faqimuh/TapSit/assets/Tuser.jpg

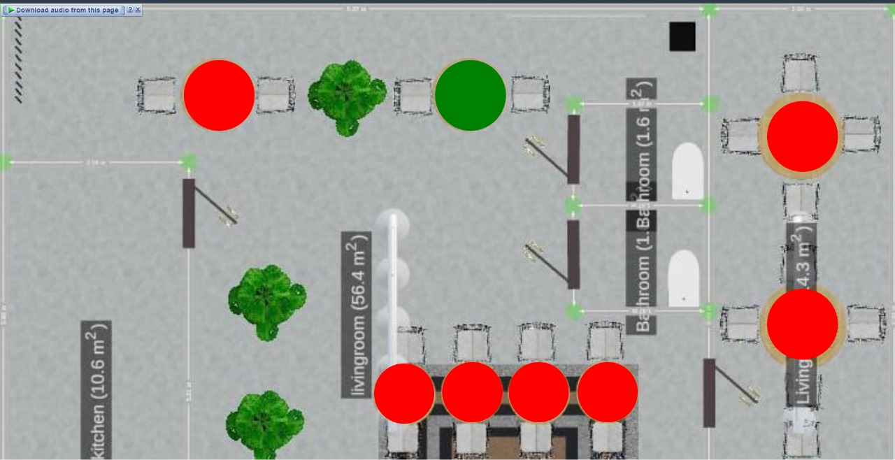
assets/Tuser.jpg
