faqimuh/TapSit/Interface UI/UX/img/about/about.png

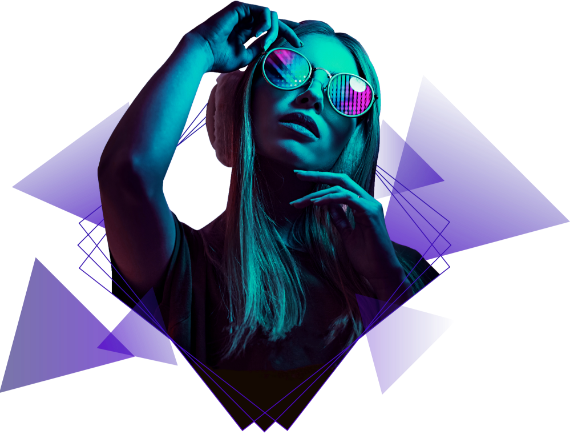
Interface UI/UX/img/about/about.png
