faqimuh/TapSit/Interface UI/UX/img/about/ap-1.jpg

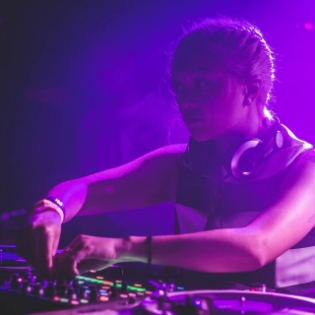
Interface UI/UX/img/about/ap-1.jpg
