faqimuh/TapSit/Interface UI/UX/img/about/ap-2.jpg

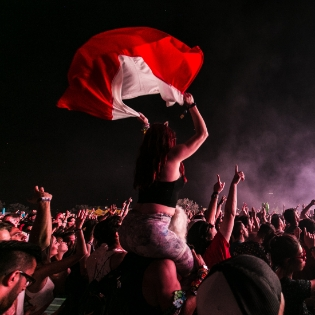
Interface UI/UX/img/about/ap-2.jpg
