faqimuh/TapSit/Interface UI/UX/img/about/ap-3.jpg

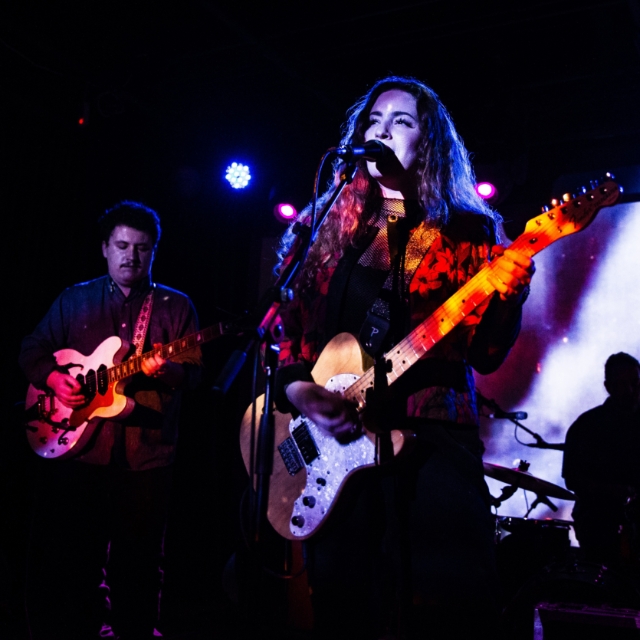
Interface UI/UX/img/about/ap-3.jpg
