faqimuh/TapSit/Interface UI/UX/img/about/ap-4.jpg

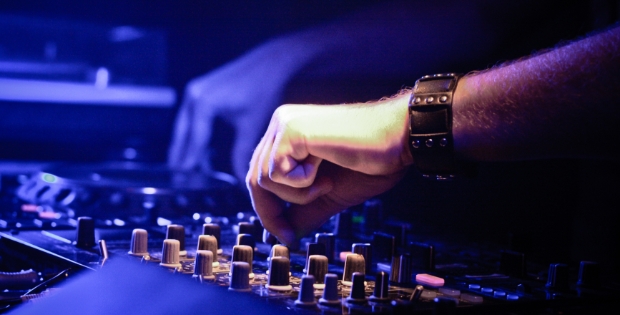
Interface UI/UX/img/about/ap-4.jpg
