faqimuh/TapSit/Interface UI/UX/img/about/ap-5.jpg

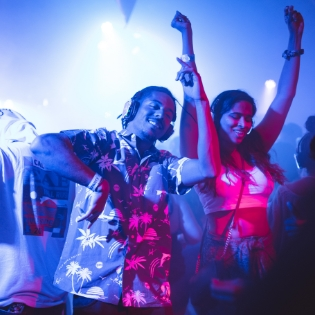
Interface UI/UX/img/about/ap-5.jpg
