faqimuh/TapSit/Interface UI/UX/img/about/ap-6.jpg

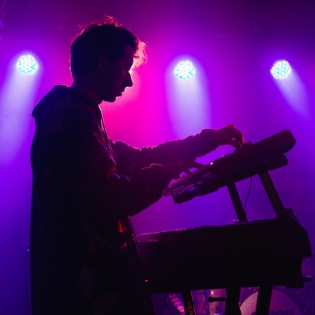
Interface UI/UX/img/about/ap-6.jpg
