faqimuh/TapSit/Interface UI/UX/img/about/ap-7.jpg

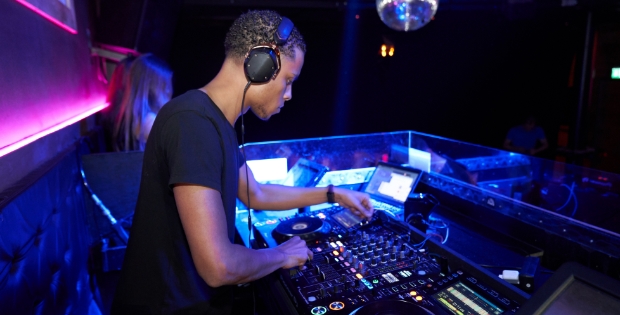
Interface UI/UX/img/about/ap-7.jpg
