faqimuh/TapSit/Interface UI/UX/img/Background.jpg

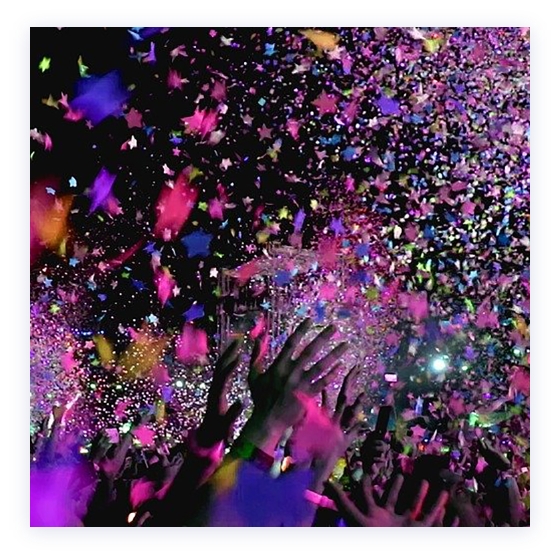
Interface UI/UX/img/Background.jpg
