faqimuh/TapSit/Interface UI/UX/img/blog/blog-1.jpg

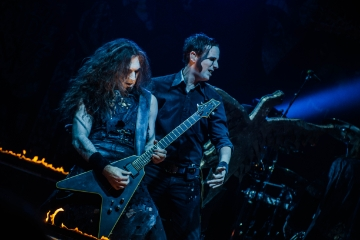
Interface UI/UX/img/blog/blog-1.jpg
