faqimuh/TapSit/Interface UI/UX/img/blog/blog-2.jpg

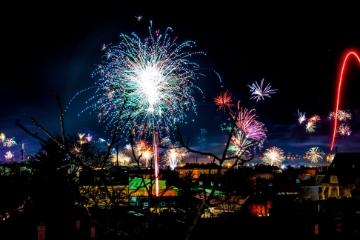
Interface UI/UX/img/blog/blog-2.jpg
