faqimuh/TapSit/Interface UI/UX/img/blog/blog-3.jpg

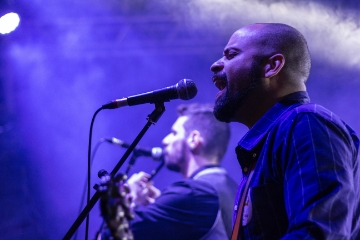
Interface UI/UX/img/blog/blog-3.jpg
