faqimuh/TapSit/Interface UI/UX/img/blog/blog-4.jpg

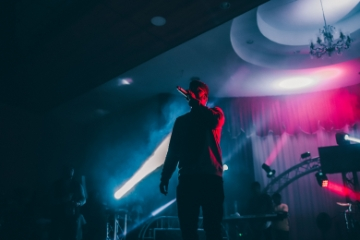
Interface UI/UX/img/blog/blog-4.jpg
