faqimuh/TapSit/Interface UI/UX/img/blog/blog-5.jpg

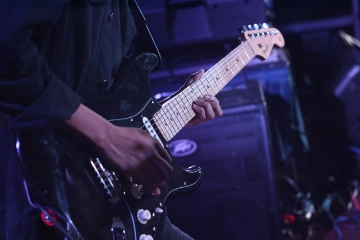
Interface UI/UX/img/blog/blog-5.jpg
