faqimuh/TapSit/Interface UI/UX/img/blog/blog-6.jpg

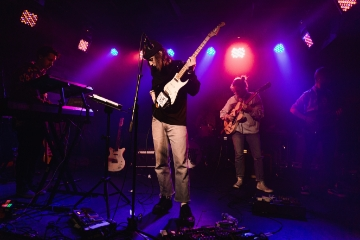
Interface UI/UX/img/blog/blog-6.jpg
