faqimuh/TapSit/Interface UI/UX/img/blog/details/bs-2.jpg

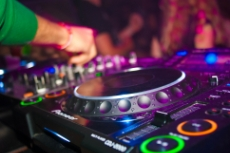
Interface UI/UX/img/blog/details/bs-2.jpg
