faqimuh/TapSit/Interface UI/UX/img/blog/details/details-pic.jpg

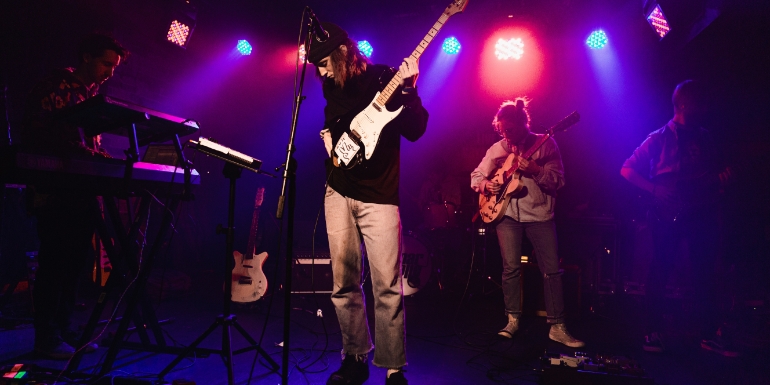
Interface UI/UX/img/blog/details/details-pic.jpg
