faqimuh/TapSit/Interface UI/UX/img/blog/large-item.jpg

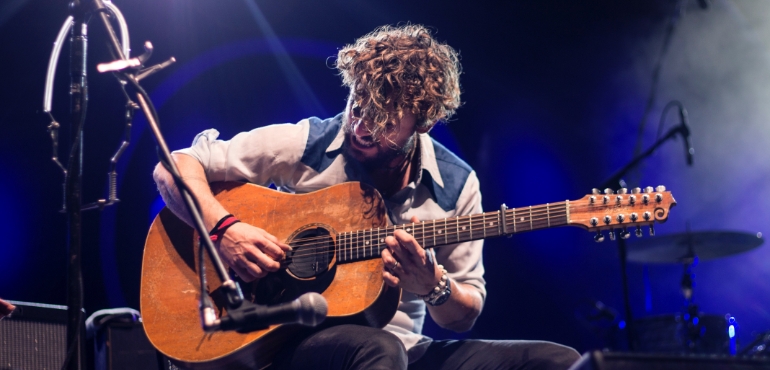
Interface UI/UX/img/blog/large-item.jpg
