faqimuh/TapSit/Interface UI/UX/img/countdown-bg.jpg

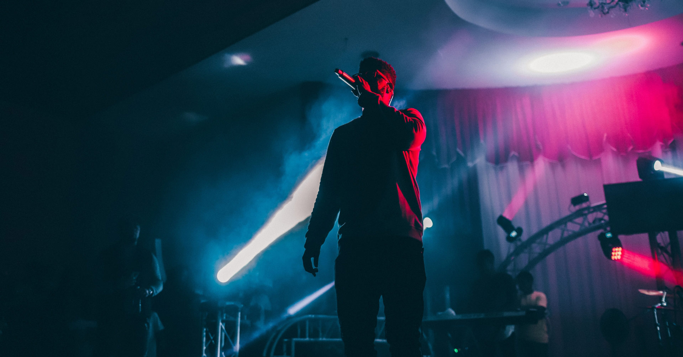
Interface UI/UX/img/countdown-bg.jpg
