faqimuh/TapSit/Interface UI/UX/img/discography/disco-1.jpg

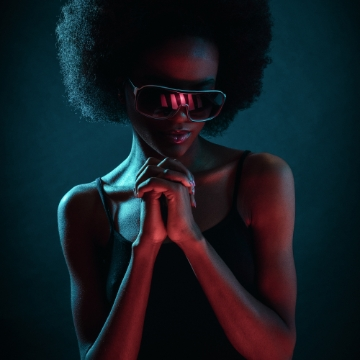
Interface UI/UX/img/discography/disco-1.jpg
