faqimuh/TapSit/Interface UI/UX/img/discography/disco-2.jpg

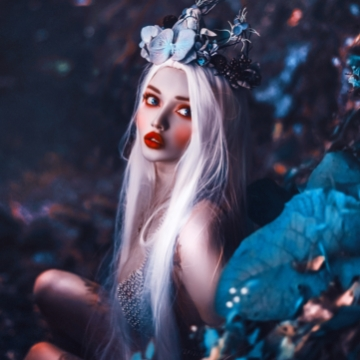
Interface UI/UX/img/discography/disco-2.jpg
