faqimuh/TapSit/Interface UI/UX/img/discography/disco-3.jpg

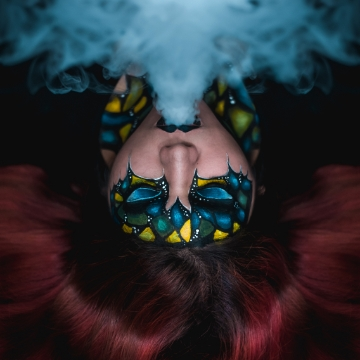
Interface UI/UX/img/discography/disco-3.jpg
