faqimuh/TapSit/Interface UI/UX/img/discography/disco-4.jpg

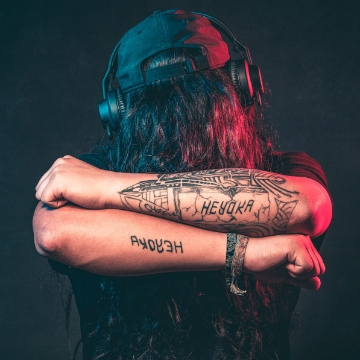
Interface UI/UX/img/discography/disco-4.jpg
