faqimuh/TapSit/Interface UI/UX/img/discography/disco-5.jpg

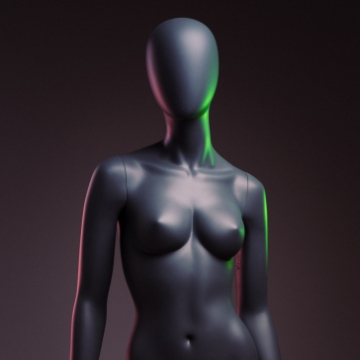
Interface UI/UX/img/discography/disco-5.jpg
