faqimuh/TapSit/Interface UI/UX/img/discography/disco-6.jpg

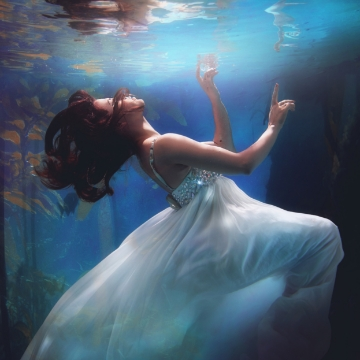
Interface UI/UX/img/discography/disco-6.jpg
