faqimuh/TapSit/Interface UI/UX/img/events/event-1.jpg

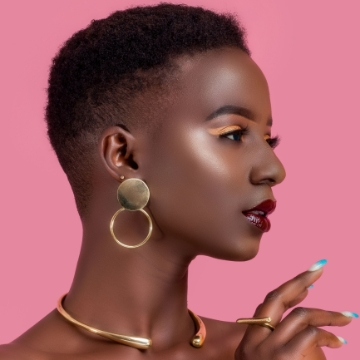
Interface UI/UX/img/events/event-1.jpg
