faqimuh/TapSit/Interface UI/UX/img/events/event-2.jpg

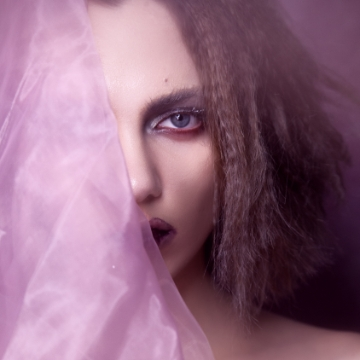
Interface UI/UX/img/events/event-2.jpg
