faqimuh/TapSit/Interface UI/UX/img/events/event-3.jpg

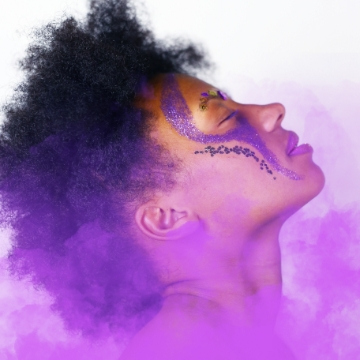
Interface UI/UX/img/events/event-3.jpg
