faqimuh/TapSit/Interface UI/UX/img/footer-bg.png

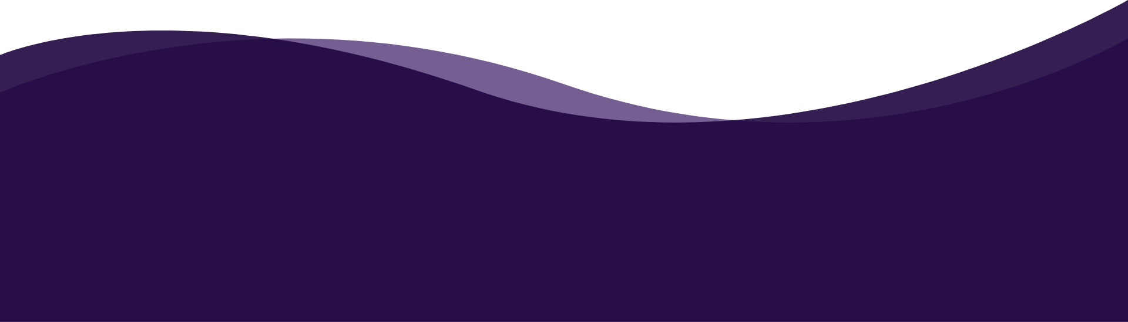
Interface UI/UX/img/footer-bg.png
