faqimuh/TapSit/Interface UI/UX/img/hero-bg.png

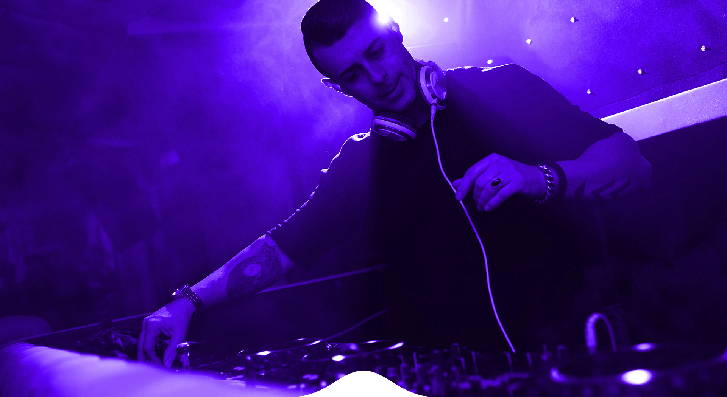
Interface UI/UX/img/hero-bg.png
