faqimuh/TapSit/Interface UI/UX/img/services/as-1.jpg

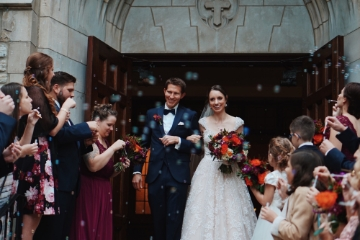
Interface UI/UX/img/services/as-1.jpg
