faqimuh/TapSit/Interface UI/UX/img/services/as-2.jpg

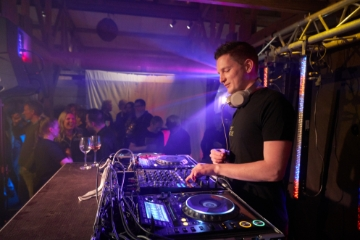
Interface UI/UX/img/services/as-2.jpg
