faqimuh/TapSit/Interface UI/UX/img/services/as-3.jpg

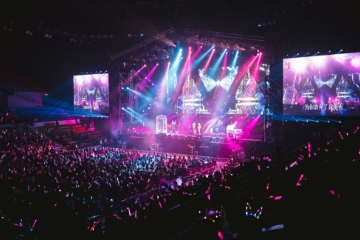
Interface UI/UX/img/services/as-3.jpg
