faqimuh/TapSit/Interface UI/UX/img/skill-video.jpg

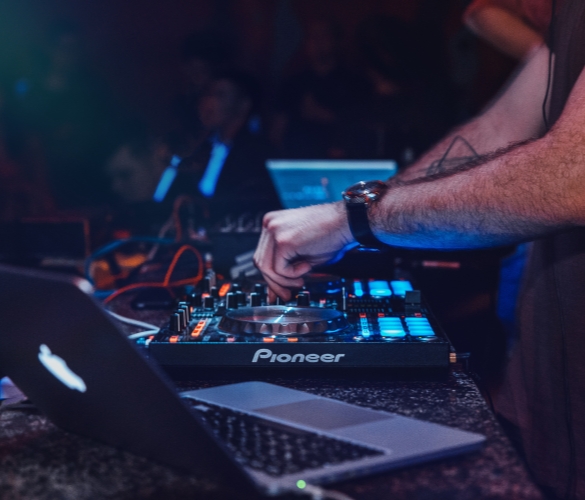
Interface UI/UX/img/skill-video.jpg
