faqimuh/TapSit/Interface UI/UX/img/tours/tour-1.jpg

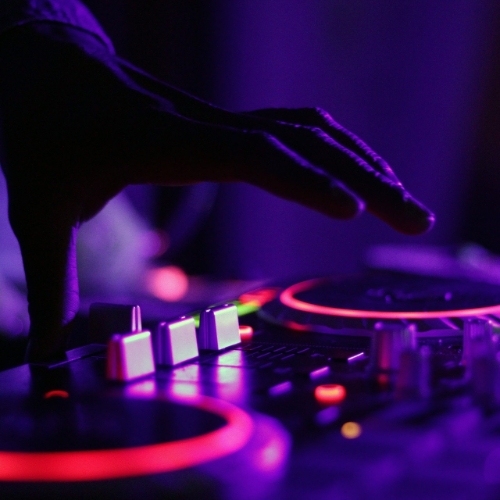
Interface UI/UX/img/tours/tour-1.jpg
