faqimuh/TapSit/Interface UI/UX/img/tours/tour-2.jpg

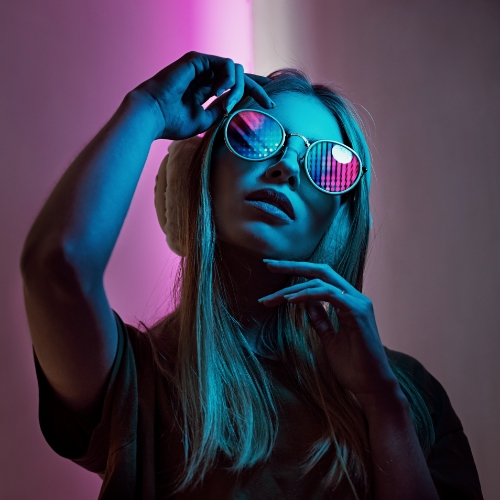
Interface UI/UX/img/tours/tour-2.jpg
