faqimuh/TapSit/Interface UI/UX/img/tours/tour-3.jpg

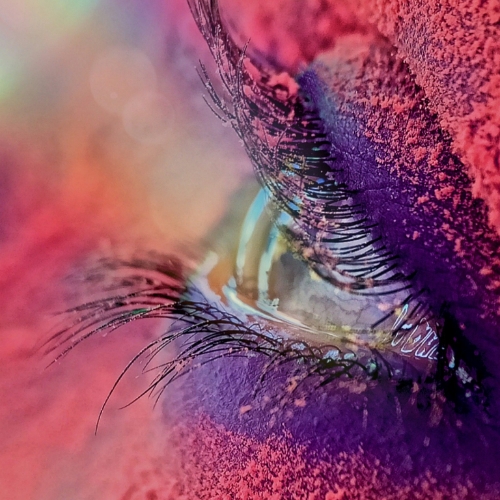
Interface UI/UX/img/tours/tour-3.jpg
