faqimuh/TapSit/Interface UI/UX/img/track-right.jpg

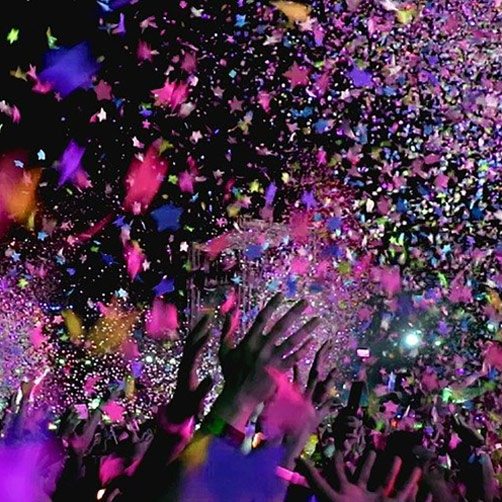
Interface UI/UX/img/track-right.jpg
