faqimuh/TapSit/Interface UI/UX/img/videos/large-item.jpg

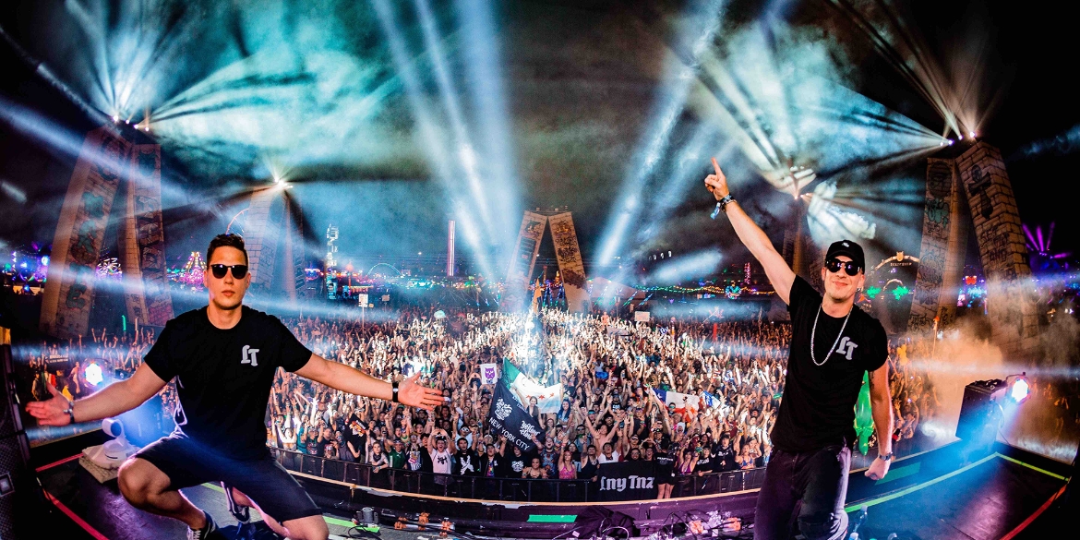
Interface UI/UX/img/videos/large-item.jpg
