faqimuh/TapSit/Interface UI/UX/img/videos/videos-1.jpg

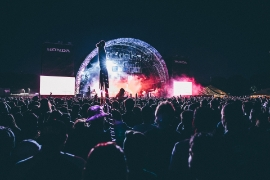
Interface UI/UX/img/videos/videos-1.jpg
