faqimuh/TapSit/Interface UI/UX/img/videos/videos-2.jpg

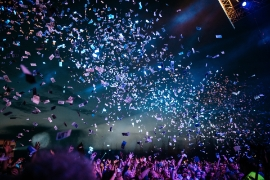
Interface UI/UX/img/videos/videos-2.jpg
