faqimuh/TapSit/Interface UI/UX/img/videos/videos-3.jpg

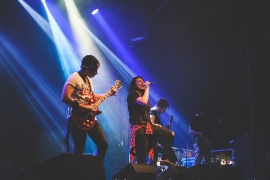
Interface UI/UX/img/videos/videos-3.jpg
