faqimuh/TapSit/Interface UI/UX/img/videos/videos-4.jpg

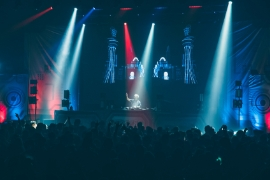
Interface UI/UX/img/videos/videos-4.jpg
