faqimuh/TapSit/Interface UI/UX/img/youtube/youtube-1.jpg

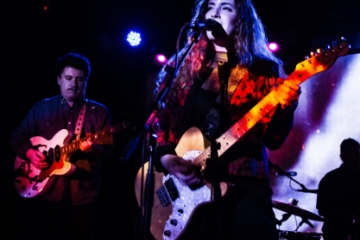
Interface UI/UX/img/youtube/youtube-1.jpg
