faqimuh/TapSit/Interface UI/UX/img/youtube/youtube-2.jpg

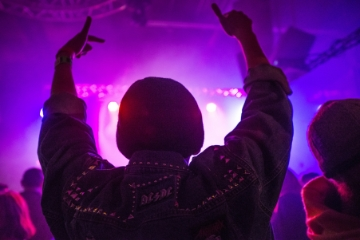
Interface UI/UX/img/youtube/youtube-2.jpg
