faqimuh/TapSit/Interface UI/UX/img/youtube/youtube-3.jpg

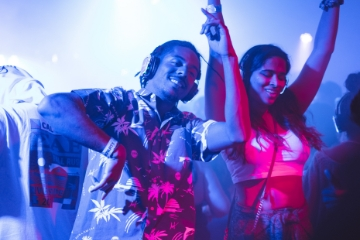
Interface UI/UX/img/youtube/youtube-3.jpg
