faqimuh/TapSit/Interface UI/UX/build/assets/img/4.png

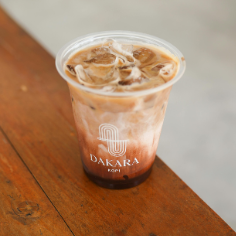
Interface UI/UX/build/assets/img/4.png
