faqimuh/TapSit/Interface UI/UX/build/assets/img/5.png

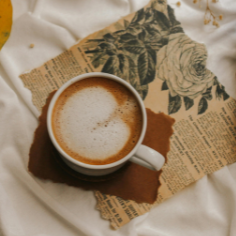
Interface UI/UX/build/assets/img/5.png
