faqimuh/TapSit/Interface UI/UX/build/assets/img/7.png

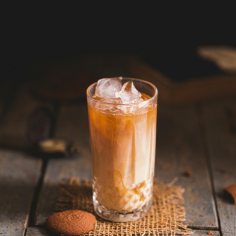
Interface UI/UX/build/assets/img/7.png
