faqimuh/TapSit/Interface UI/UX/build/assets/img/adib1.jpg

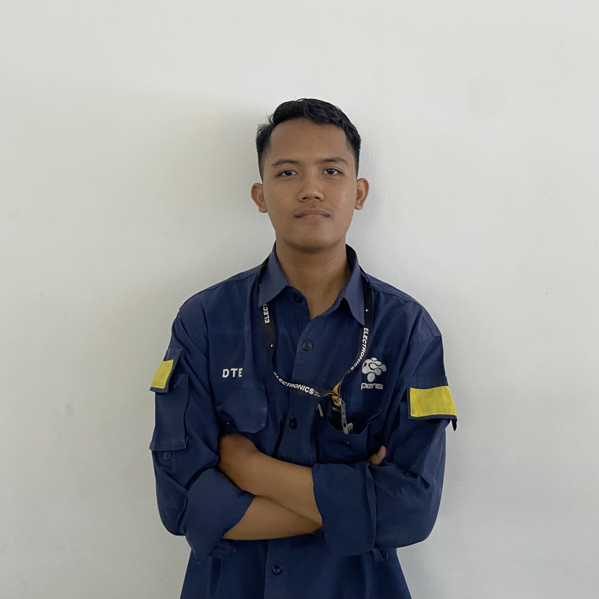
Interface UI/UX/build/assets/img/adib1.jpg
