faqimuh/TapSit/Interface UI/UX/build/assets/img/bruce-mars.jpg

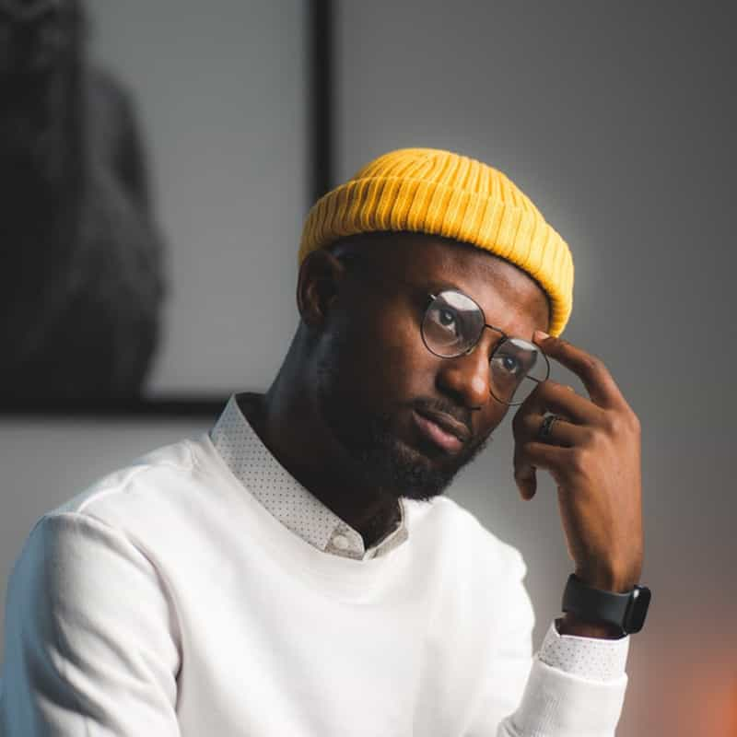
Interface UI/UX/build/assets/img/bruce-mars.jpg
