faqimuh/TapSit/Interface UI/UX/build/assets/img/c1.jpg

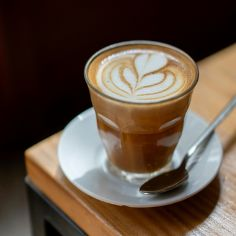
Interface UI/UX/build/assets/img/c1.jpg
