faqimuh/TapSit/Interface UI/UX/build/assets/img/c2.jpg

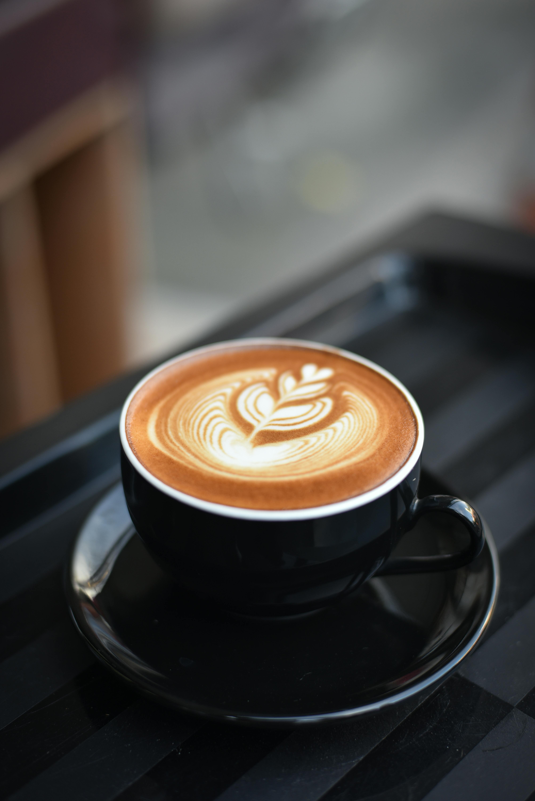
Interface UI/UX/build/assets/img/c2.jpg
