faqimuh/TapSit/Interface UI/UX/build/assets/img/constructions.jpg

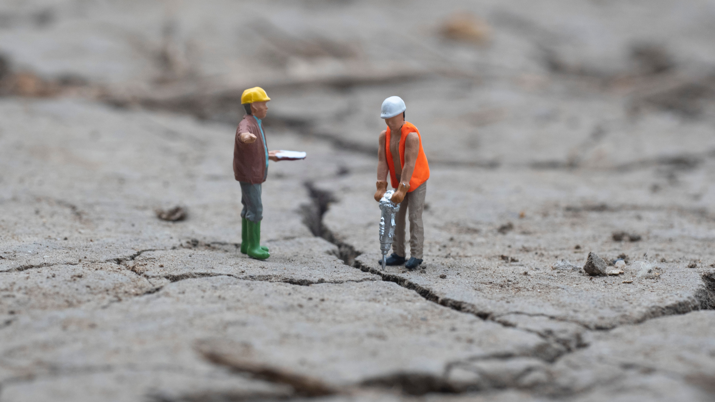
Interface UI/UX/build/assets/img/constructions.jpg
