faqimuh/TapSit/Interface UI/UX/build/assets/img/curved-images/coffe.jpg

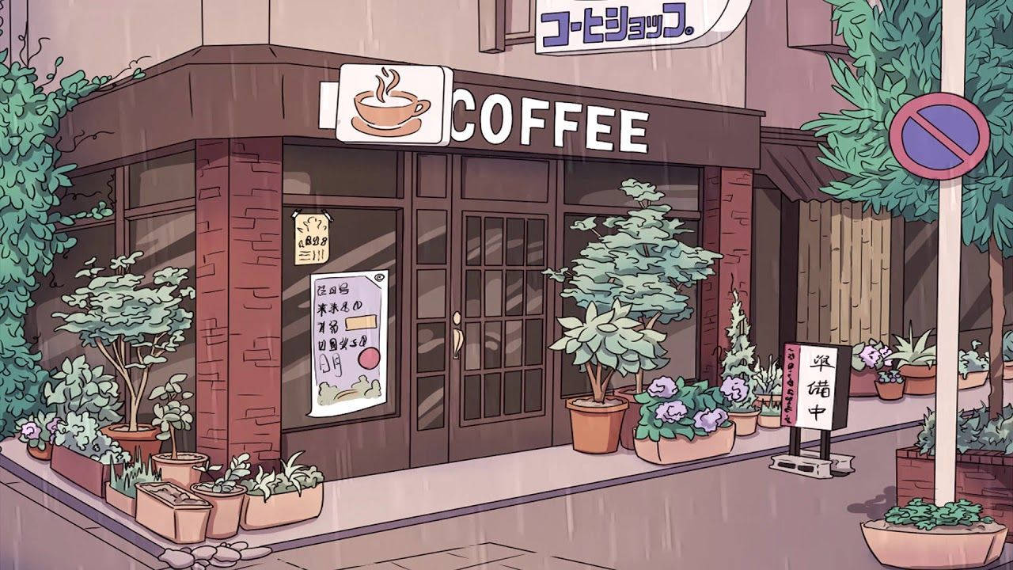
Interface UI/UX/build/assets/img/curved-images/coffe.jpg
