faqimuh/TapSit/Interface UI/UX/build/assets/img/curved-images/curved0.jpg

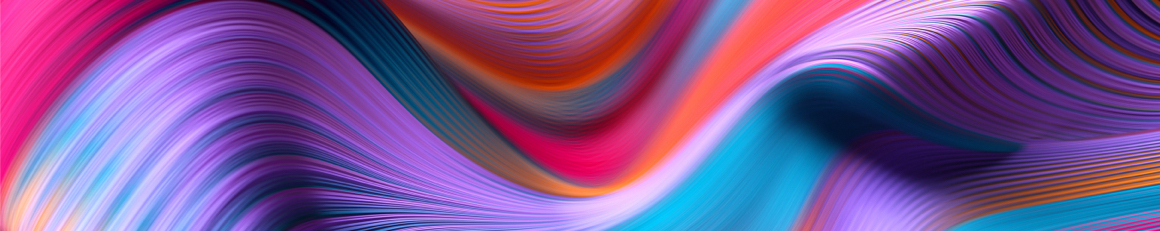
Interface UI/UX/build/assets/img/curved-images/curved0.jpg
