faqimuh/TapSit/Interface UI/UX/build/assets/img/curved-images/curved1.jpg

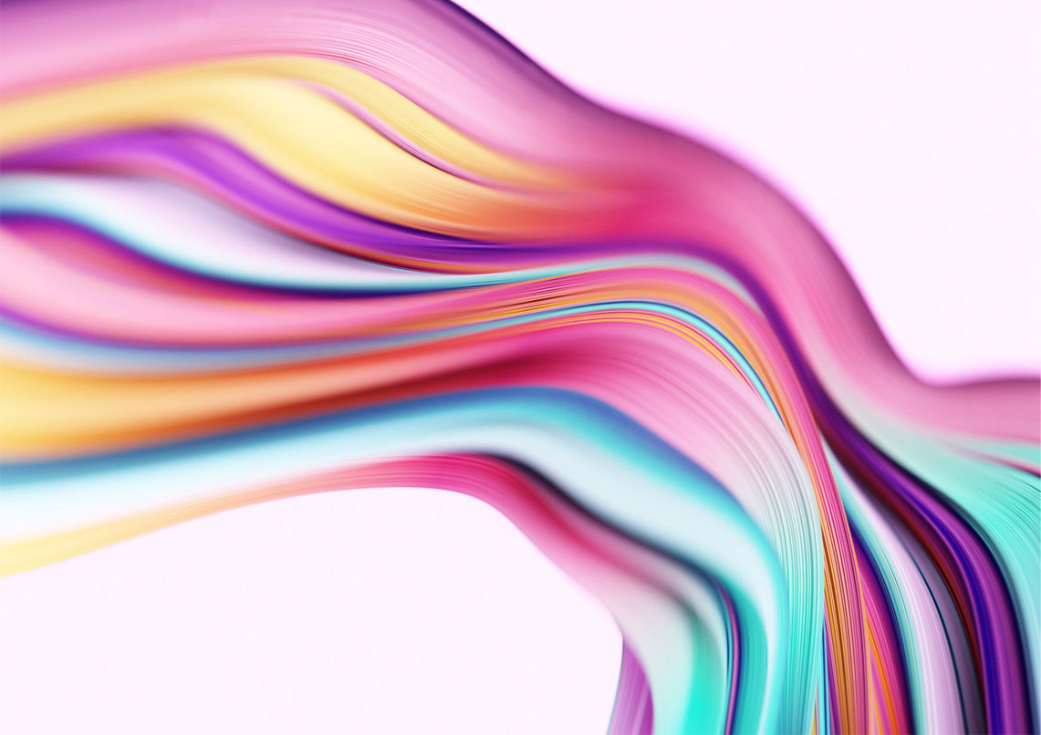
Interface UI/UX/build/assets/img/curved-images/curved1.jpg
