faqimuh/TapSit/Interface UI/UX/build/assets/img/curved-images/curved6.jpg

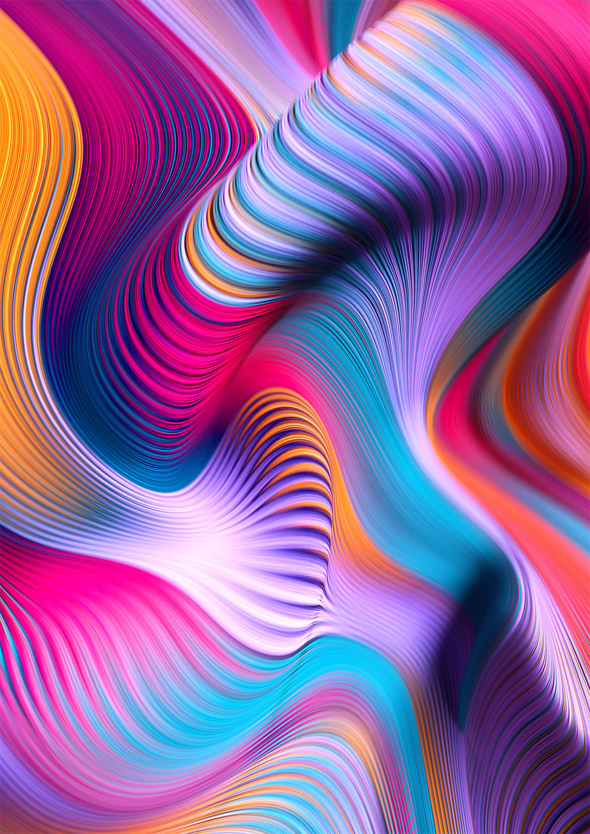
Interface UI/UX/build/assets/img/curved-images/curved6.jpg
