faqimuh/TapSit/Interface UI/UX/build/assets/img/curved-images/curved8.jpg

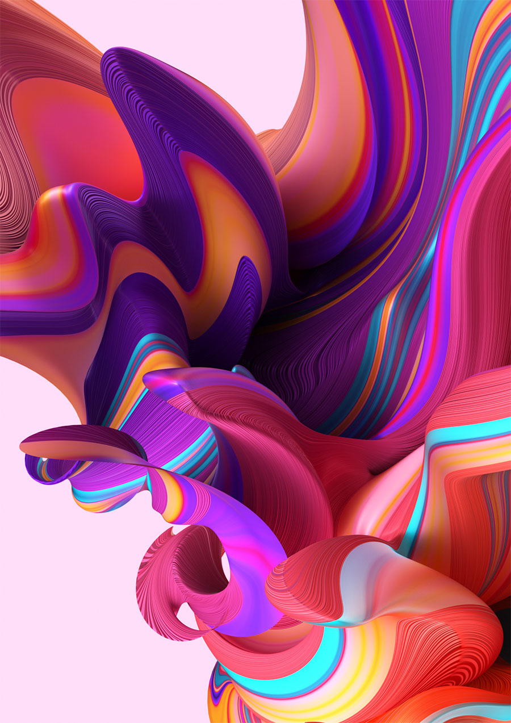
Interface UI/UX/build/assets/img/curved-images/curved8.jpg
