faqimuh/TapSit/Interface UI/UX/build/assets/img/curved-images/curved14.jpg

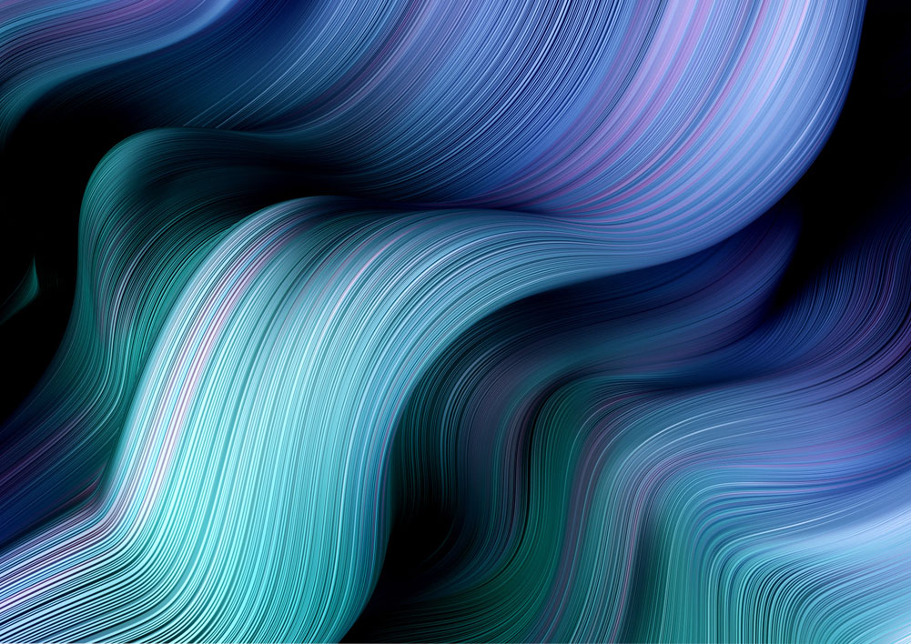
Interface UI/UX/build/assets/img/curved-images/curved14.jpg
