faqimuh/TapSit/Interface UI/UX/build/assets/img/curved-images/denah1.jpeg

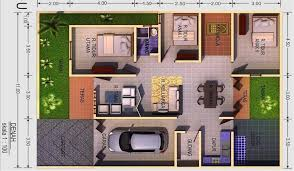
Interface UI/UX/build/assets/img/curved-images/denah1.jpeg
