faqimuh/TapSit/Interface UI/UX/build/assets/img/curved-images/maps1.jpg

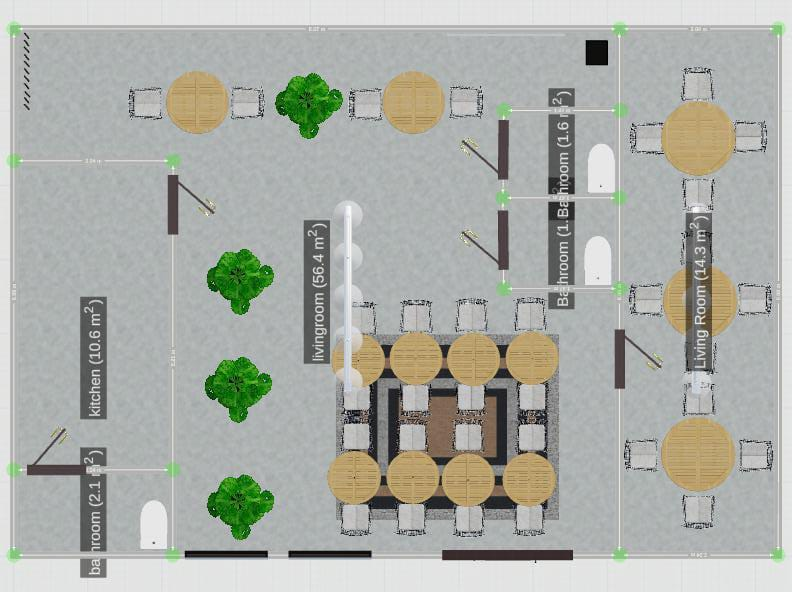
Interface UI/UX/build/assets/img/curved-images/maps1.jpg
