faqimuh/TapSit/Interface UI/UX/build/assets/img/curved-images/maps2.jpg

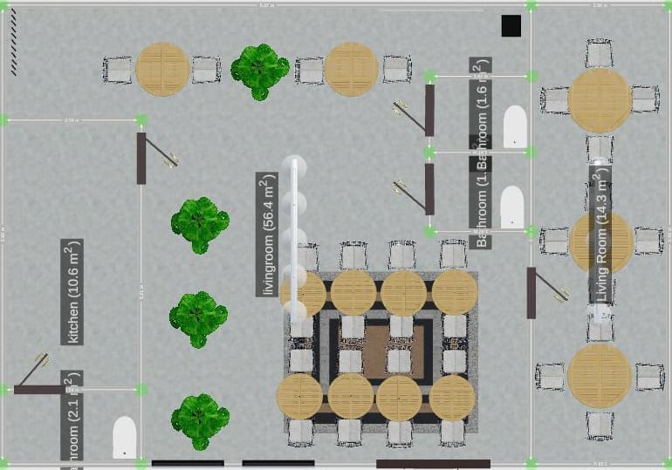
Interface UI/UX/build/assets/img/curved-images/maps2.jpg
