faqimuh/TapSit/Interface UI/UX/build/assets/img/curved-images/white-curved.jpeg

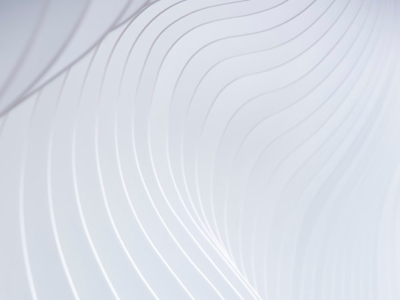
Interface UI/UX/build/assets/img/curved-images/white-curved.jpeg
