faqimuh/TapSit/Interface UI/UX/build/assets/img/home-decor-1.jpg

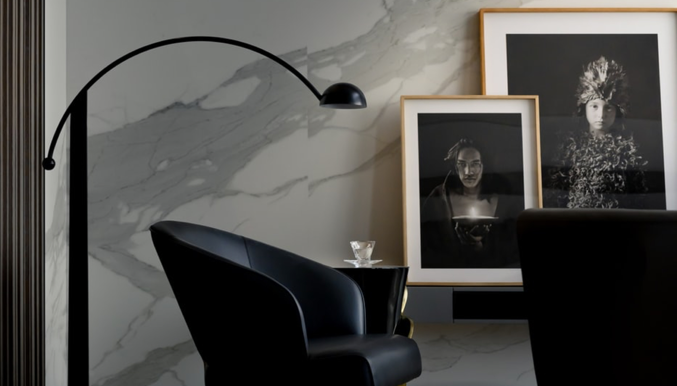
Interface UI/UX/build/assets/img/home-decor-1.jpg
