faqimuh/TapSit/Interface UI/UX/build/assets/img/home-decor-2.jpg

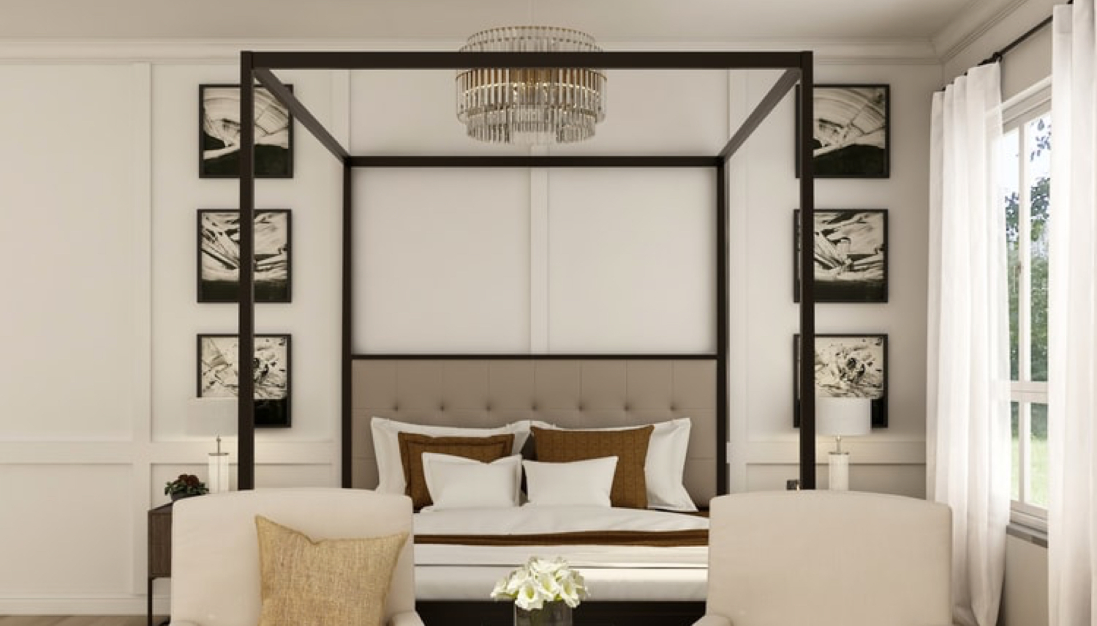
Interface UI/UX/build/assets/img/home-decor-2.jpg
