faqimuh/TapSit/Interface UI/UX/build/assets/img/home-decor-3.jpg

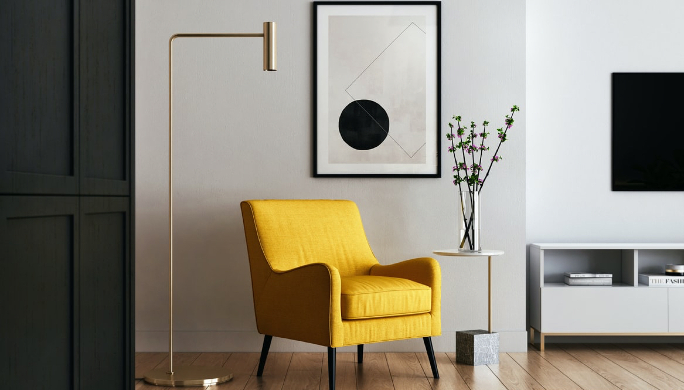
Interface UI/UX/build/assets/img/home-decor-3.jpg
