faqimuh/TapSit/Interface UI/UX/build/assets/img/illustrations/rocket-white.png

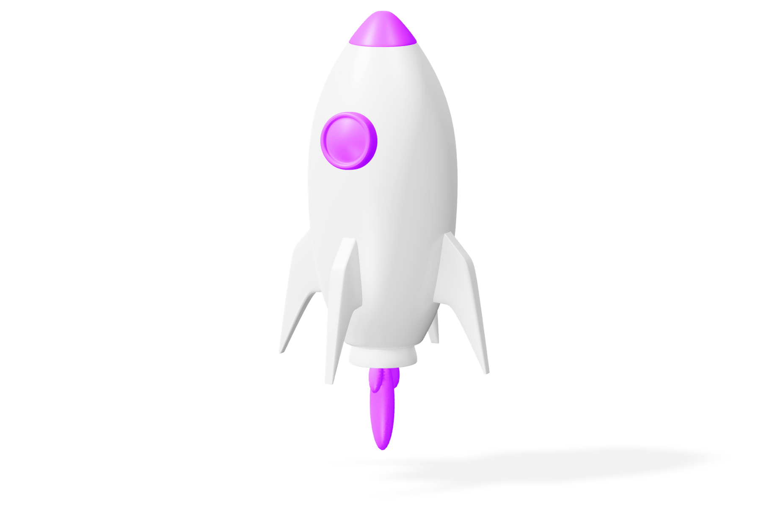
Interface UI/UX/build/assets/img/illustrations/rocket-white.png
