faqimuh/TapSit/Interface UI/UX/build/assets/img/ivana-square.jpg

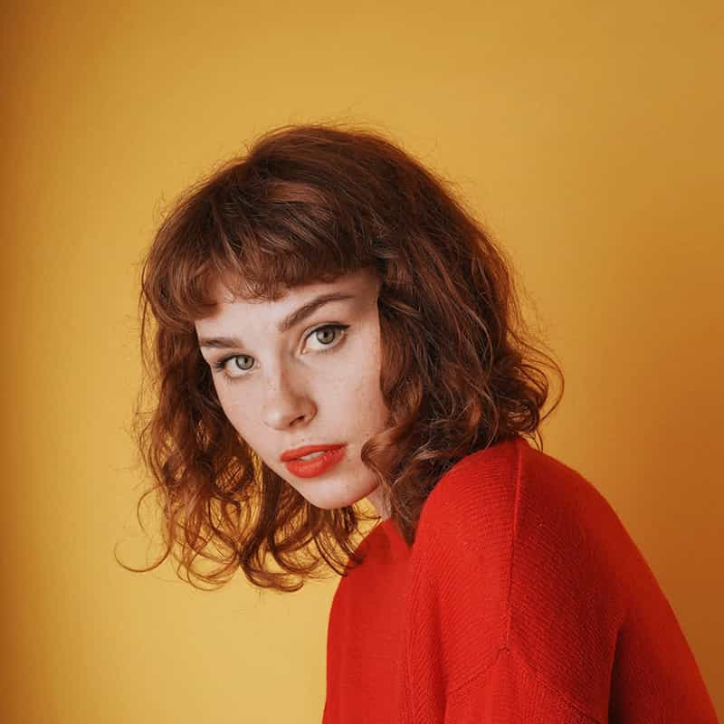
Interface UI/UX/build/assets/img/ivana-square.jpg
