faqimuh/TapSit/Interface UI/UX/build/assets/img/ivancik.jpg

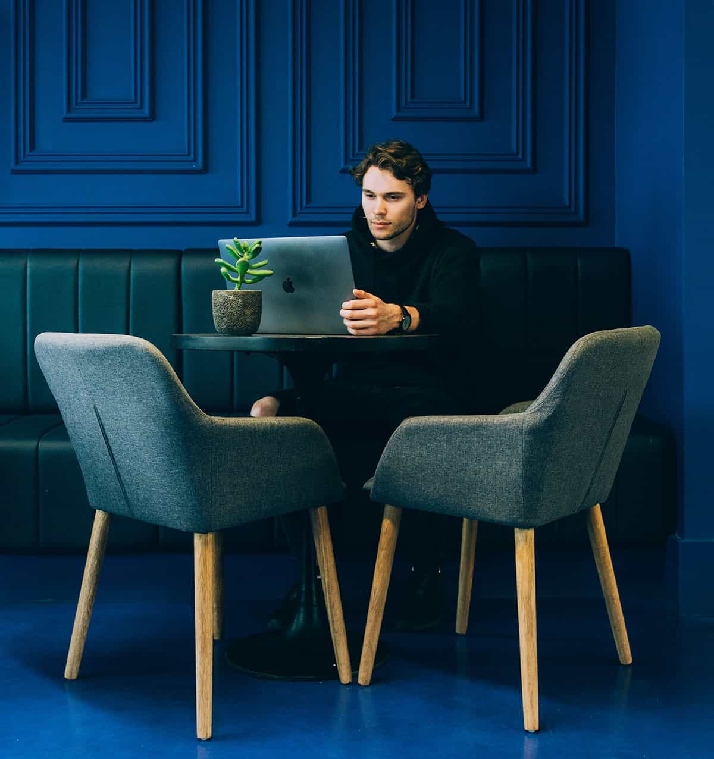
Interface UI/UX/build/assets/img/ivancik.jpg
