faqimuh/TapSit/Interface UI/UX/build/assets/img/kal-visuals-square.jpg

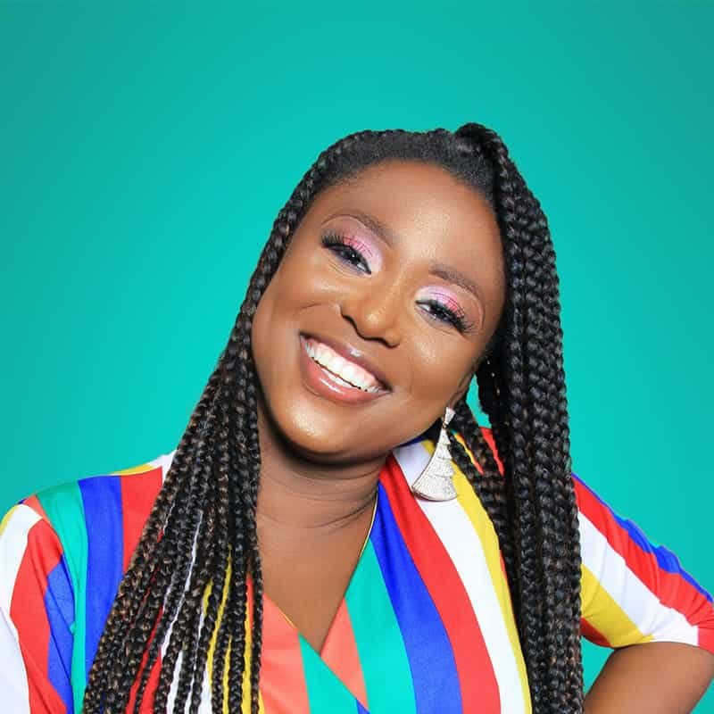
Interface UI/UX/build/assets/img/kal-visuals-square.jpg
