faqimuh/TapSit/Interface UI/UX/build/assets/img/LT1.jpg

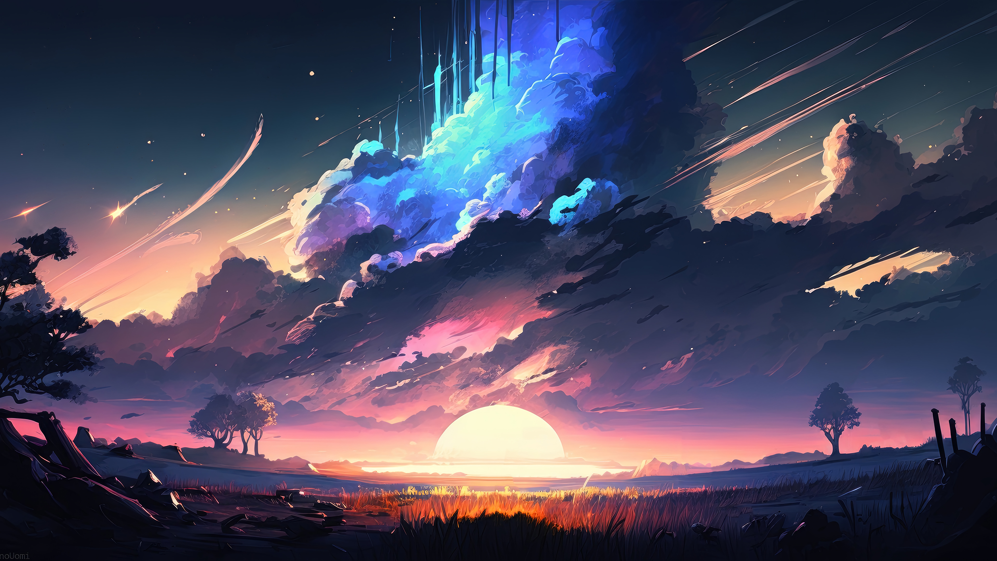
Interface UI/UX/build/assets/img/LT1.jpg
