faqimuh/TapSit/Interface UI/UX/build/assets/img/LT2.jpg

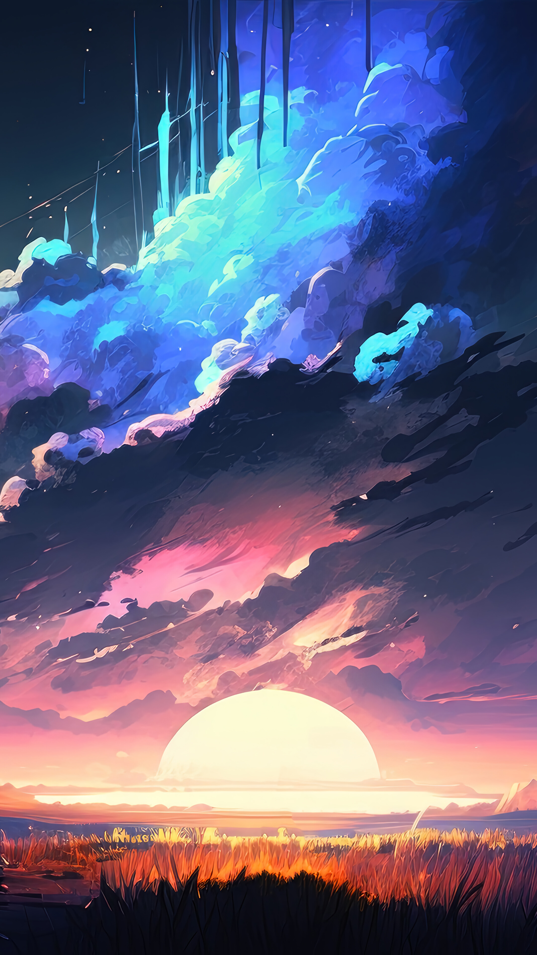
Interface UI/UX/build/assets/img/LT2.jpg
