faqimuh/TapSit/Interface UI/UX/build/assets/img/lukman.jpg

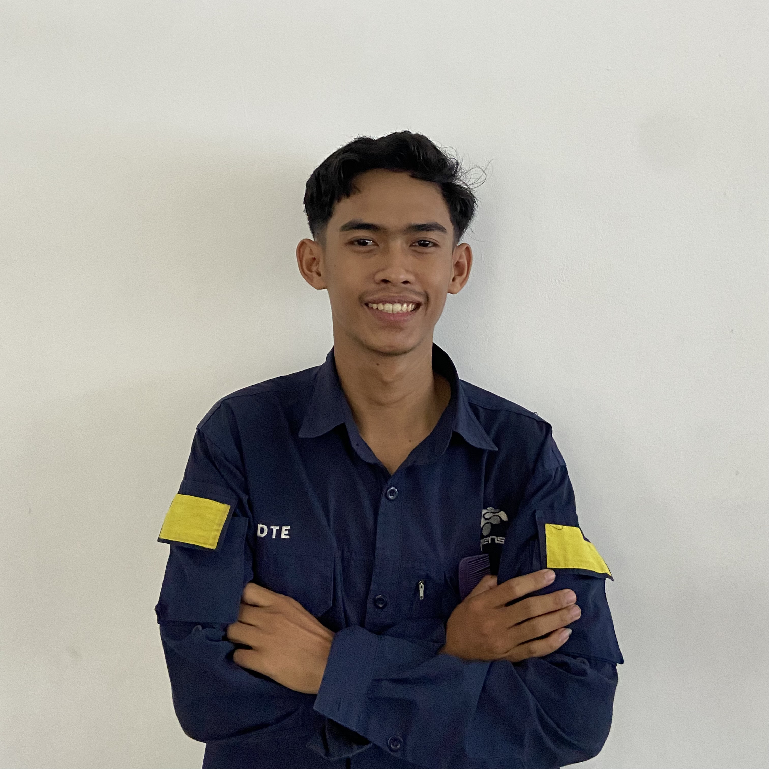
Interface UI/UX/build/assets/img/lukman.jpg
