faqimuh/TapSit/Interface UI/UX/build/assets/img/marie.jpg

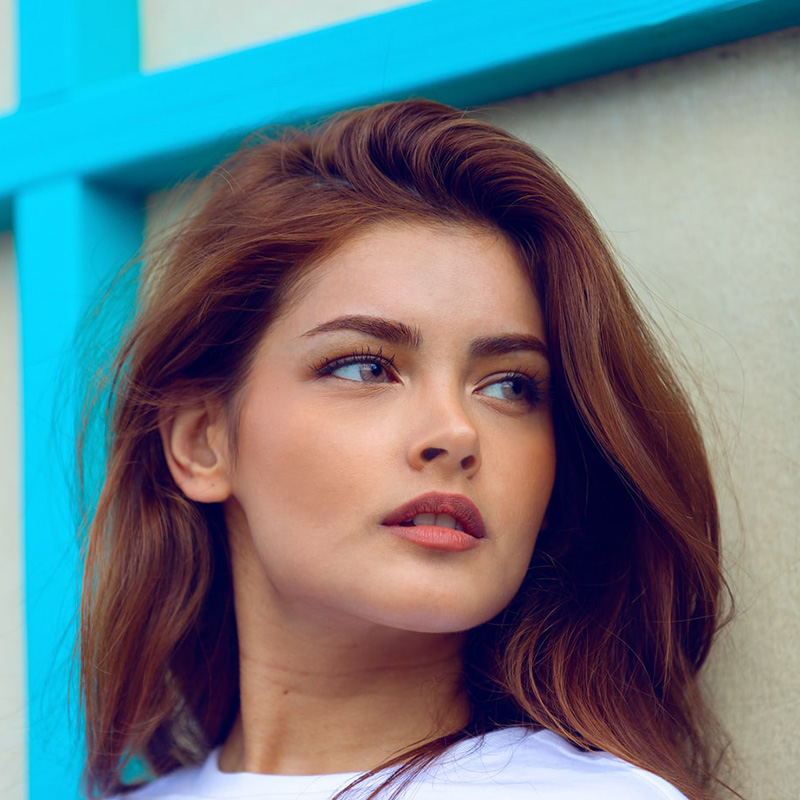
Interface UI/UX/build/assets/img/marie.jpg
