faqimuh/TapSit/Interface UI/UX/build/assets/img/team-1.jpg

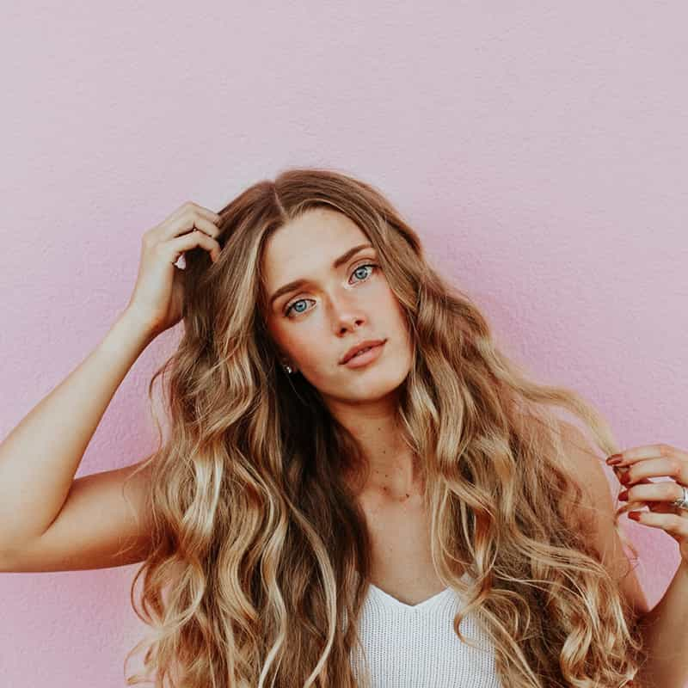
Interface UI/UX/build/assets/img/team-1.jpg
