faqimuh/TapSit/Interface UI/UX/build/assets/img/team-2.jpg

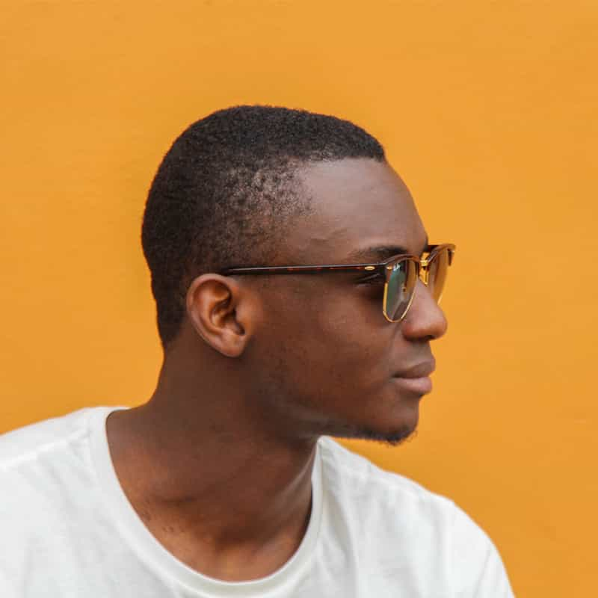
Interface UI/UX/build/assets/img/team-2.jpg
