faqimuh/TapSit/Interface UI/UX/build/assets/img/team-3.jpg

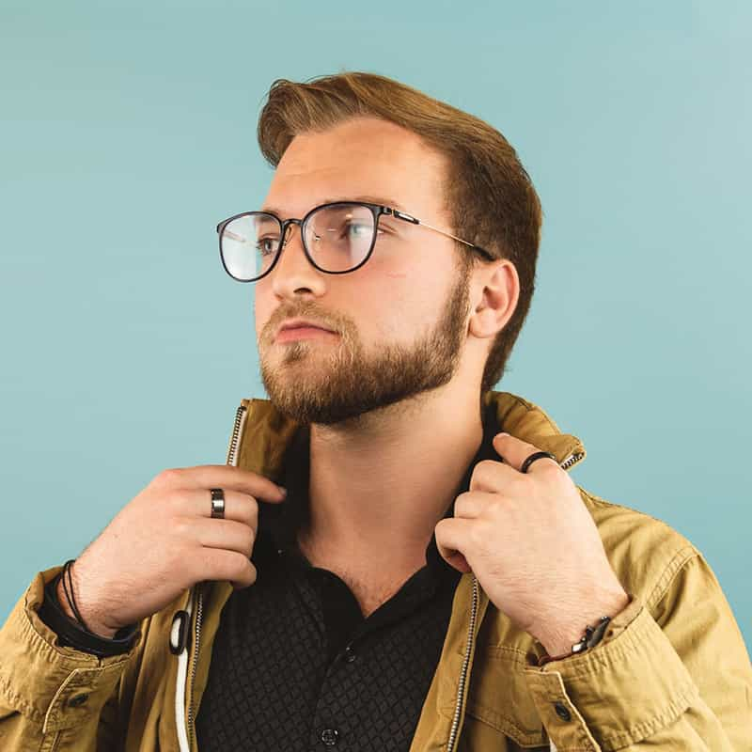
Interface UI/UX/build/assets/img/team-3.jpg
