faqimuh/TapSit/Interface UI/UX/build/assets/img/team-4.jpg

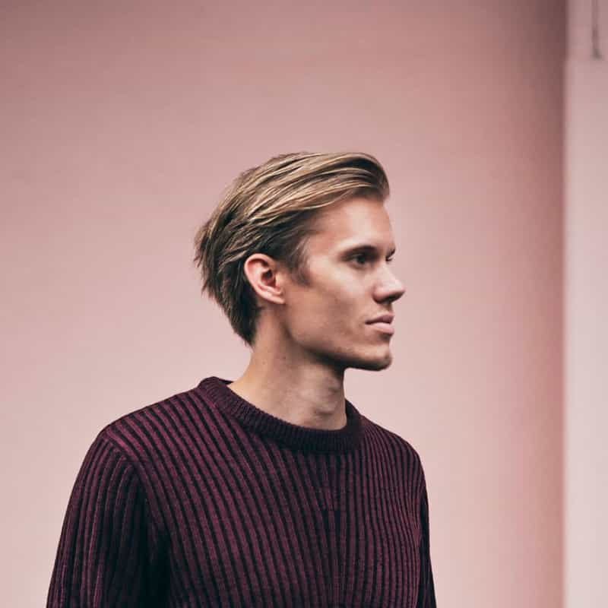
Interface UI/UX/build/assets/img/team-4.jpg
