faqimuh/TapSit/Interface UI/UX/build/assets/img/teamtapsit.jpg

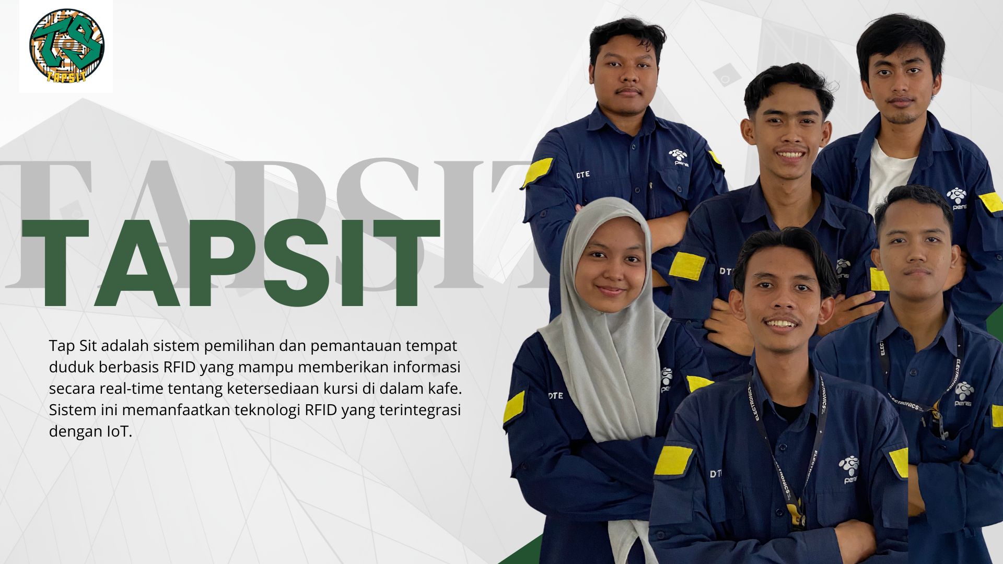
Interface UI/UX/build/assets/img/teamtapsit.jpg
