faqimuh/TapSit/Interface UI/UX/build/assets/img/vr-bg.jpg

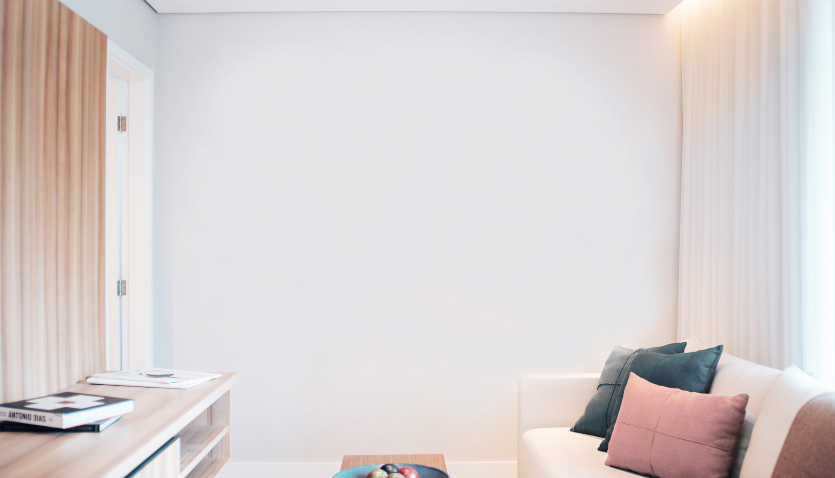
Interface UI/UX/build/assets/img/vr-bg.jpg
