faqimuh/TapSit/Interface UI/UX/build/assets/img/w1.jpg

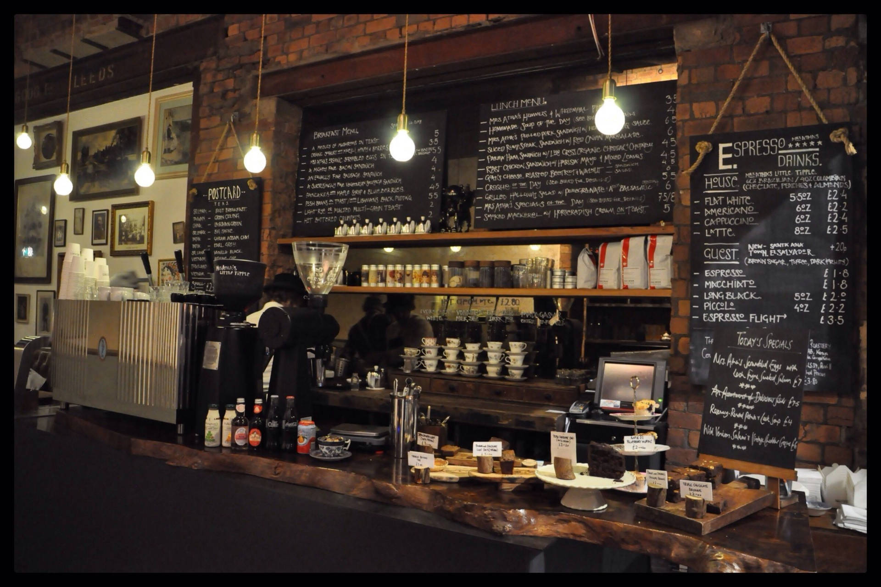
Interface UI/UX/build/assets/img/w1.jpg
