faqimuh/TapSit/Interface UI/UX/build/assets/img/zen.jpg

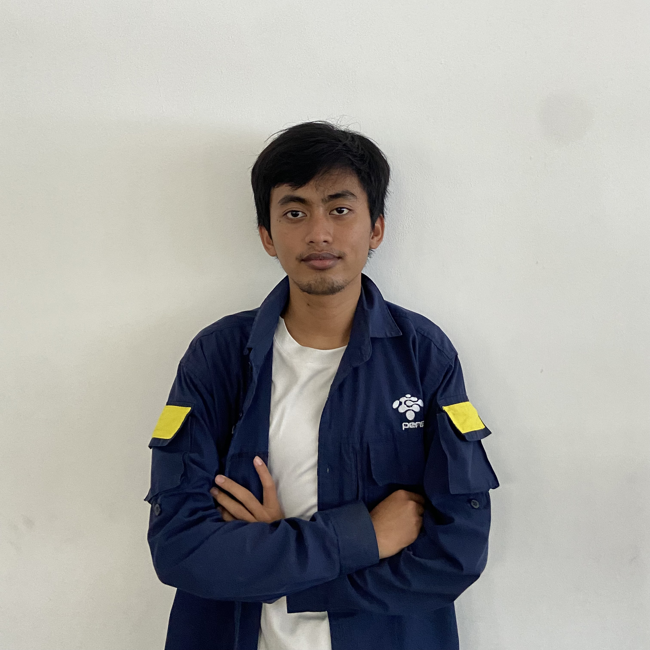
Interface UI/UX/build/assets/img/zen.jpg
