faqimuh/TapSit/Interface UI/UX/build/assets/img/faqi.jpg

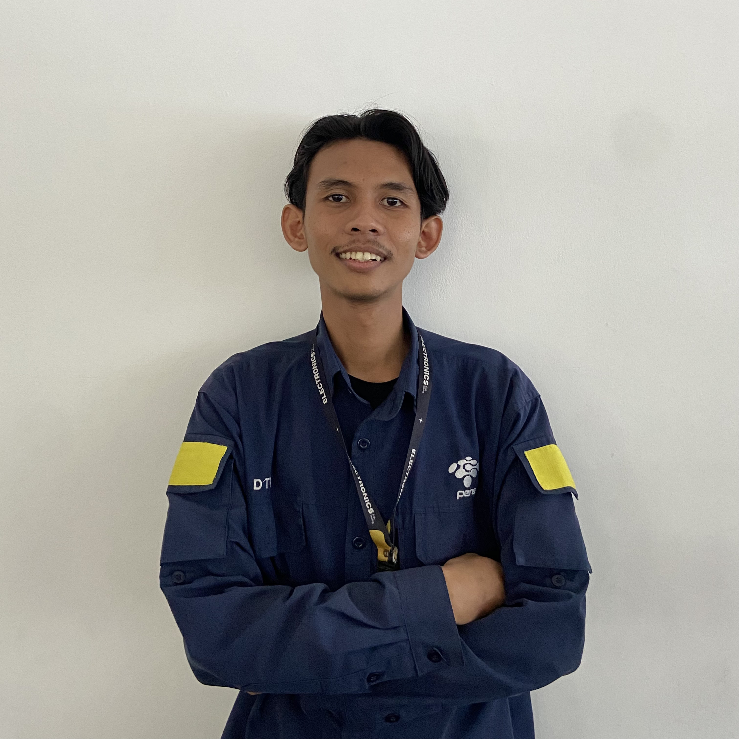
Interface UI/UX/build/assets/img/faqi.jpg
